bosco-drg/Sound-Level-Meter/simulation/sound_level_meter_SPICE.asc

C1: cap; 22µ
C2: cap; 4.7µ
C3: cap; 400n
C4: cap; 22µ
C5: cap; 22µ
Cmic: cap; 10µ
D7: LED
D8: LED
D9: LED
D10: LED
EM100T: voltage
J1: njf; J113
J2: njf; J113
Q1: npn; 2N2222
Q2: npn; 2N2222
Q16: npn; 2N2222
Q17: pnp; 2N2907
Q18: npn; 2N2222
Q19: pnp; 2N2907
Q20: npn; 2N2222
Q21: pnp; 2N2907
Q23: pnp; 2N2907
R1: res; 1Meg
R2: res; 1k
R3: res; 22k
R4: res; 2.2k
R5: res; 4.7k
R6: res; 100
R7: res; 100k
R8: res; 10k
R9: res; 12k
R10: res; 470
R11: res; 1Meg
R12: res; 1k
R13: res; 1Meg
R14: res; 1Meg
R20: res; 39.10k
R21: res; 17.902k
R22: res; 6.760k
R23: res; 9.98k
R26: res; 560k
R27: res; 470
R28: res; 560k
R29: res; 470
R30: res; 560k
R31: res; 470
R32: npn; 2N2222
R33: res; 470
R41: res; 560k
Rmic: res; 1k
Schotky1: schottky; 1N5817
V1: voltage; 9
Named nets: +Vcc, 0, Js
.tran 0 1 995m
step param f 20 120 20
Vmic
3.17E-03
1.78E-03
1.00E-03
5.63E-04
3.17E-04
